colebarach/crt_xy_monitor/hardware/crt/crt.kicad_pcb

## KiCad design sch/Z80proto1(suspend)/Z80proto1_IOboard.kicad_sch

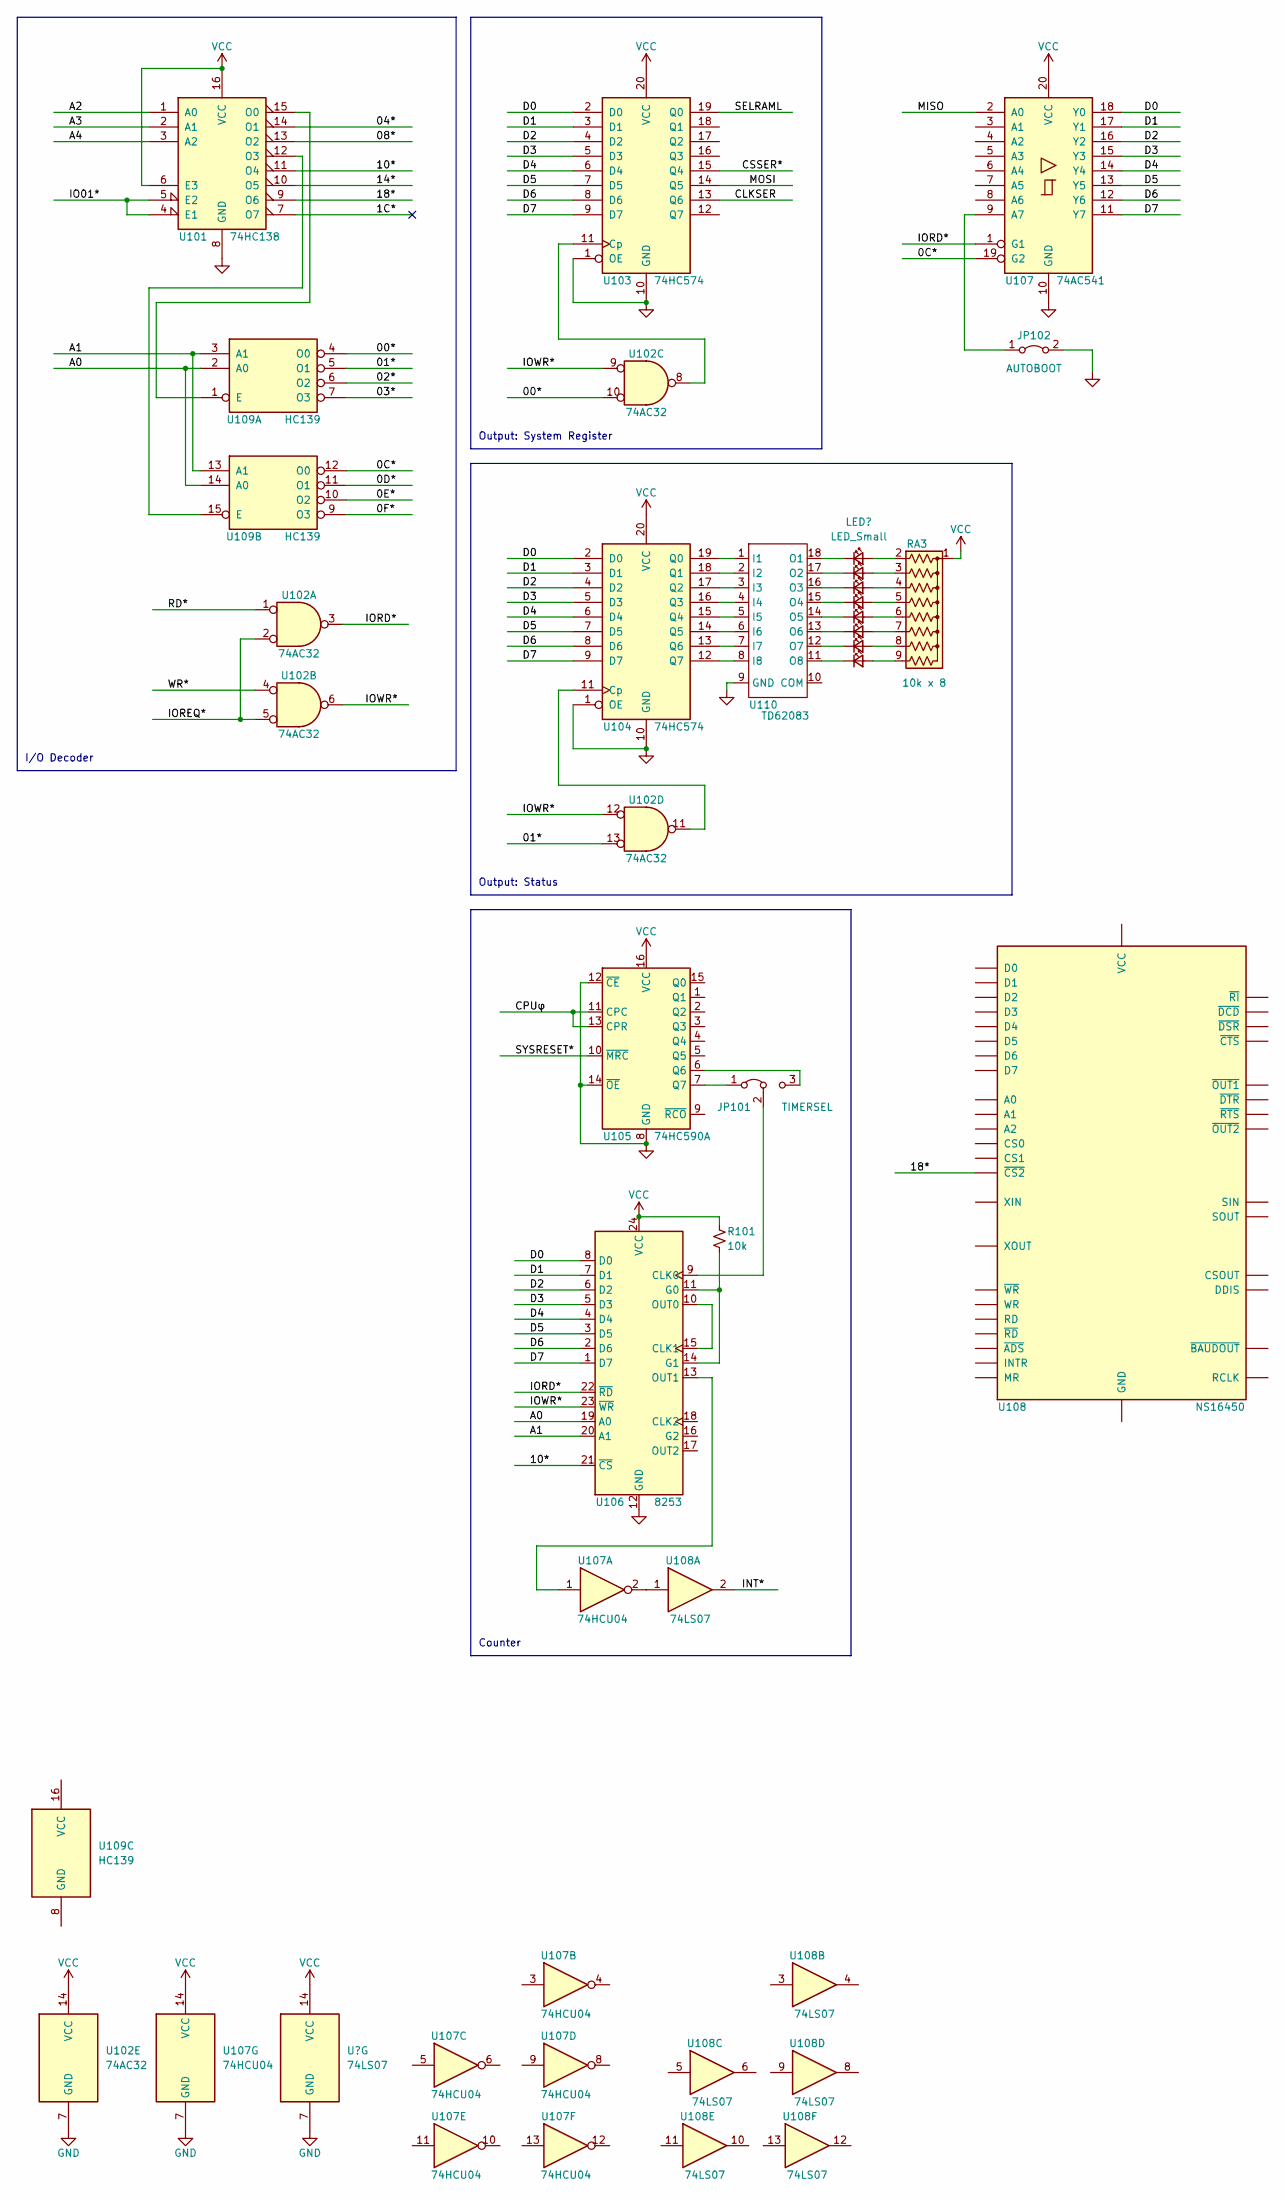
[picture p9: schematic Z80proto1_IOboard.kicad_sch]

Parts:
JP101: TIMERSEL
JP102: AUTOBOOT
R101: 10k
RA3: 10k x 8; R_Array_SIP9
U101: 74HC138
U102: 74AC32
U103, U104: 74HC574
U105: 74HC590A
U106: 8253; DIP-24_W15.24mm
U107: 74AC541
U108: 74LS07
U109: HC139
U110: TD62083

Connections:
00*: U102.10, U109.4 (O0)
0C*: U107.19 (G2), U109.12 (O0)
0D*: U109.11 (O1)
0E*: U109.10 (O2)
0F*: U109.9 (O3)
01*: U102.13, U109.5 (O1)
1C*: U101.7 (O7)
02*: U109.6 (O2)
03*: U109.7 (O3)
04*: U101.14 (O1)
08*: U101.13 (O2)
10*: U101.11 (O4), U106.21 (~CS)
14*: U101.10 (O5)
18*: U101.9 (O6), U108.14 (VCC)
A0: U106.19 (A0), U109.2 (A0), U109.14 (A0)
A1: U106.20 (A1), U109.3 (A1), U109.13 (A1)
A2: U101.1 (A0)
A3: U101.2 (A1)
A4: U101.3 (A2)
CLKSER: U103.13 (Q6)
CPUφ: U105.11 (CPC), U105.13 (CPR)
CSSER*: U103.15 (Q4)
D0: U103.2 (D0), U104.2 (D0), U106.8 (D0), U107.18 (Y0)
D1: U103.3 (D1), U104.3 (D1), U106.7 (D1), U107.17 (Y1)
D2: U103.4 (D2), U104.4 (D2), U106.6 (D2), U107.16 (Y2)
D3: U103.5 (D3), U104.5 (D3), U106.5 (D3), U107.15 (Y3)
D4: U103.6 (D4), U104.6 (D4), U106.4 (D4), U107.14 (VCC)
D5: U103.7 (D5), U104.7 (D5), U106.3 (D5), U107.13
D6: U103.8 (D6), U104.8 (D6), U106.2 (D6), U107.12
D7: U103.9 (D7), U104.9 (D7), U106.1 (D7), U107.11
INT*: U108.2
IO01*: U101.4 (E1), U101.5 (E2)
IORD*: U102.3, U106.22 (~RD), U107.1
IOREQ*: U102.2, U102.5
IOWR*: U102.6, U102.9, U102.12, U106.23 (~WR)
MISO: U107.2
MOSI: U103.14 (Q5)
unnamed: JP101.1 (A), U105.7 (Q7)
unnamed: JP101.2 (C), U106.9 (CLK0)
unnamed: JP101.3 (B), U105.6 (Q6)
unnamed: JP102.1 (A), U107.9
unnamed: R101.1, U106.24 (VCC)
unnamed: R101.2, U106.11 (G0), U106.14 (G1)
unnamed: U101.12 (O3), U109.15 (E)
unnamed: U101.15 (O0), U109.1 (E)
unnamed: U101.6 (E3), U101.16 (VCC)
unnamed: U102.8, U103.11 (Cp)
unnamed: U102.11, U104.11 (Cp)
unnamed: U103.1 (OE), U103.10 (GND)
unnamed: U104.1 (OE), U104.10 (GND)
unnamed: U104.12 (Q7), U110.8 (I8)
unnamed: U104.13 (Q6), U110.7 (I7)
unnamed: U104.14 (Q5), U110.6 (I6)
unnamed: U104.15 (Q4), U110.5 (I5)
unnamed: U104.16 (Q3), U110.4 (I4)
unnamed: U104.17 (Q2), U110.3 (I3)
unnamed: U104.18 (Q1), U110.2 (I2)
unnamed: U104.19 (Q0), U110.1 (I1)
unnamed: U105.8 (GND), U105.12 (~CE), U105.14 (~OE)
unnamed: U106.10 (OUT0), U106.15 (CLK1)
unnamed: U106.13 (OUT1), U107.1
unnamed: U107.2, U108.1
RD*: U102.1
SELRAML: U103.19 (Q0)
SYSRESET*: U105.10 (~MRC)
WR*: U102.4

Notes on the sheet:
Output: Status
I/O Decoder
Output: System Register
Counter
