colebarach/crt_xy_monitor/hardware/crt/crt.kicad_pcb

## KiCad design sch/Z80proto2/FDC_DMA.kicad_sch

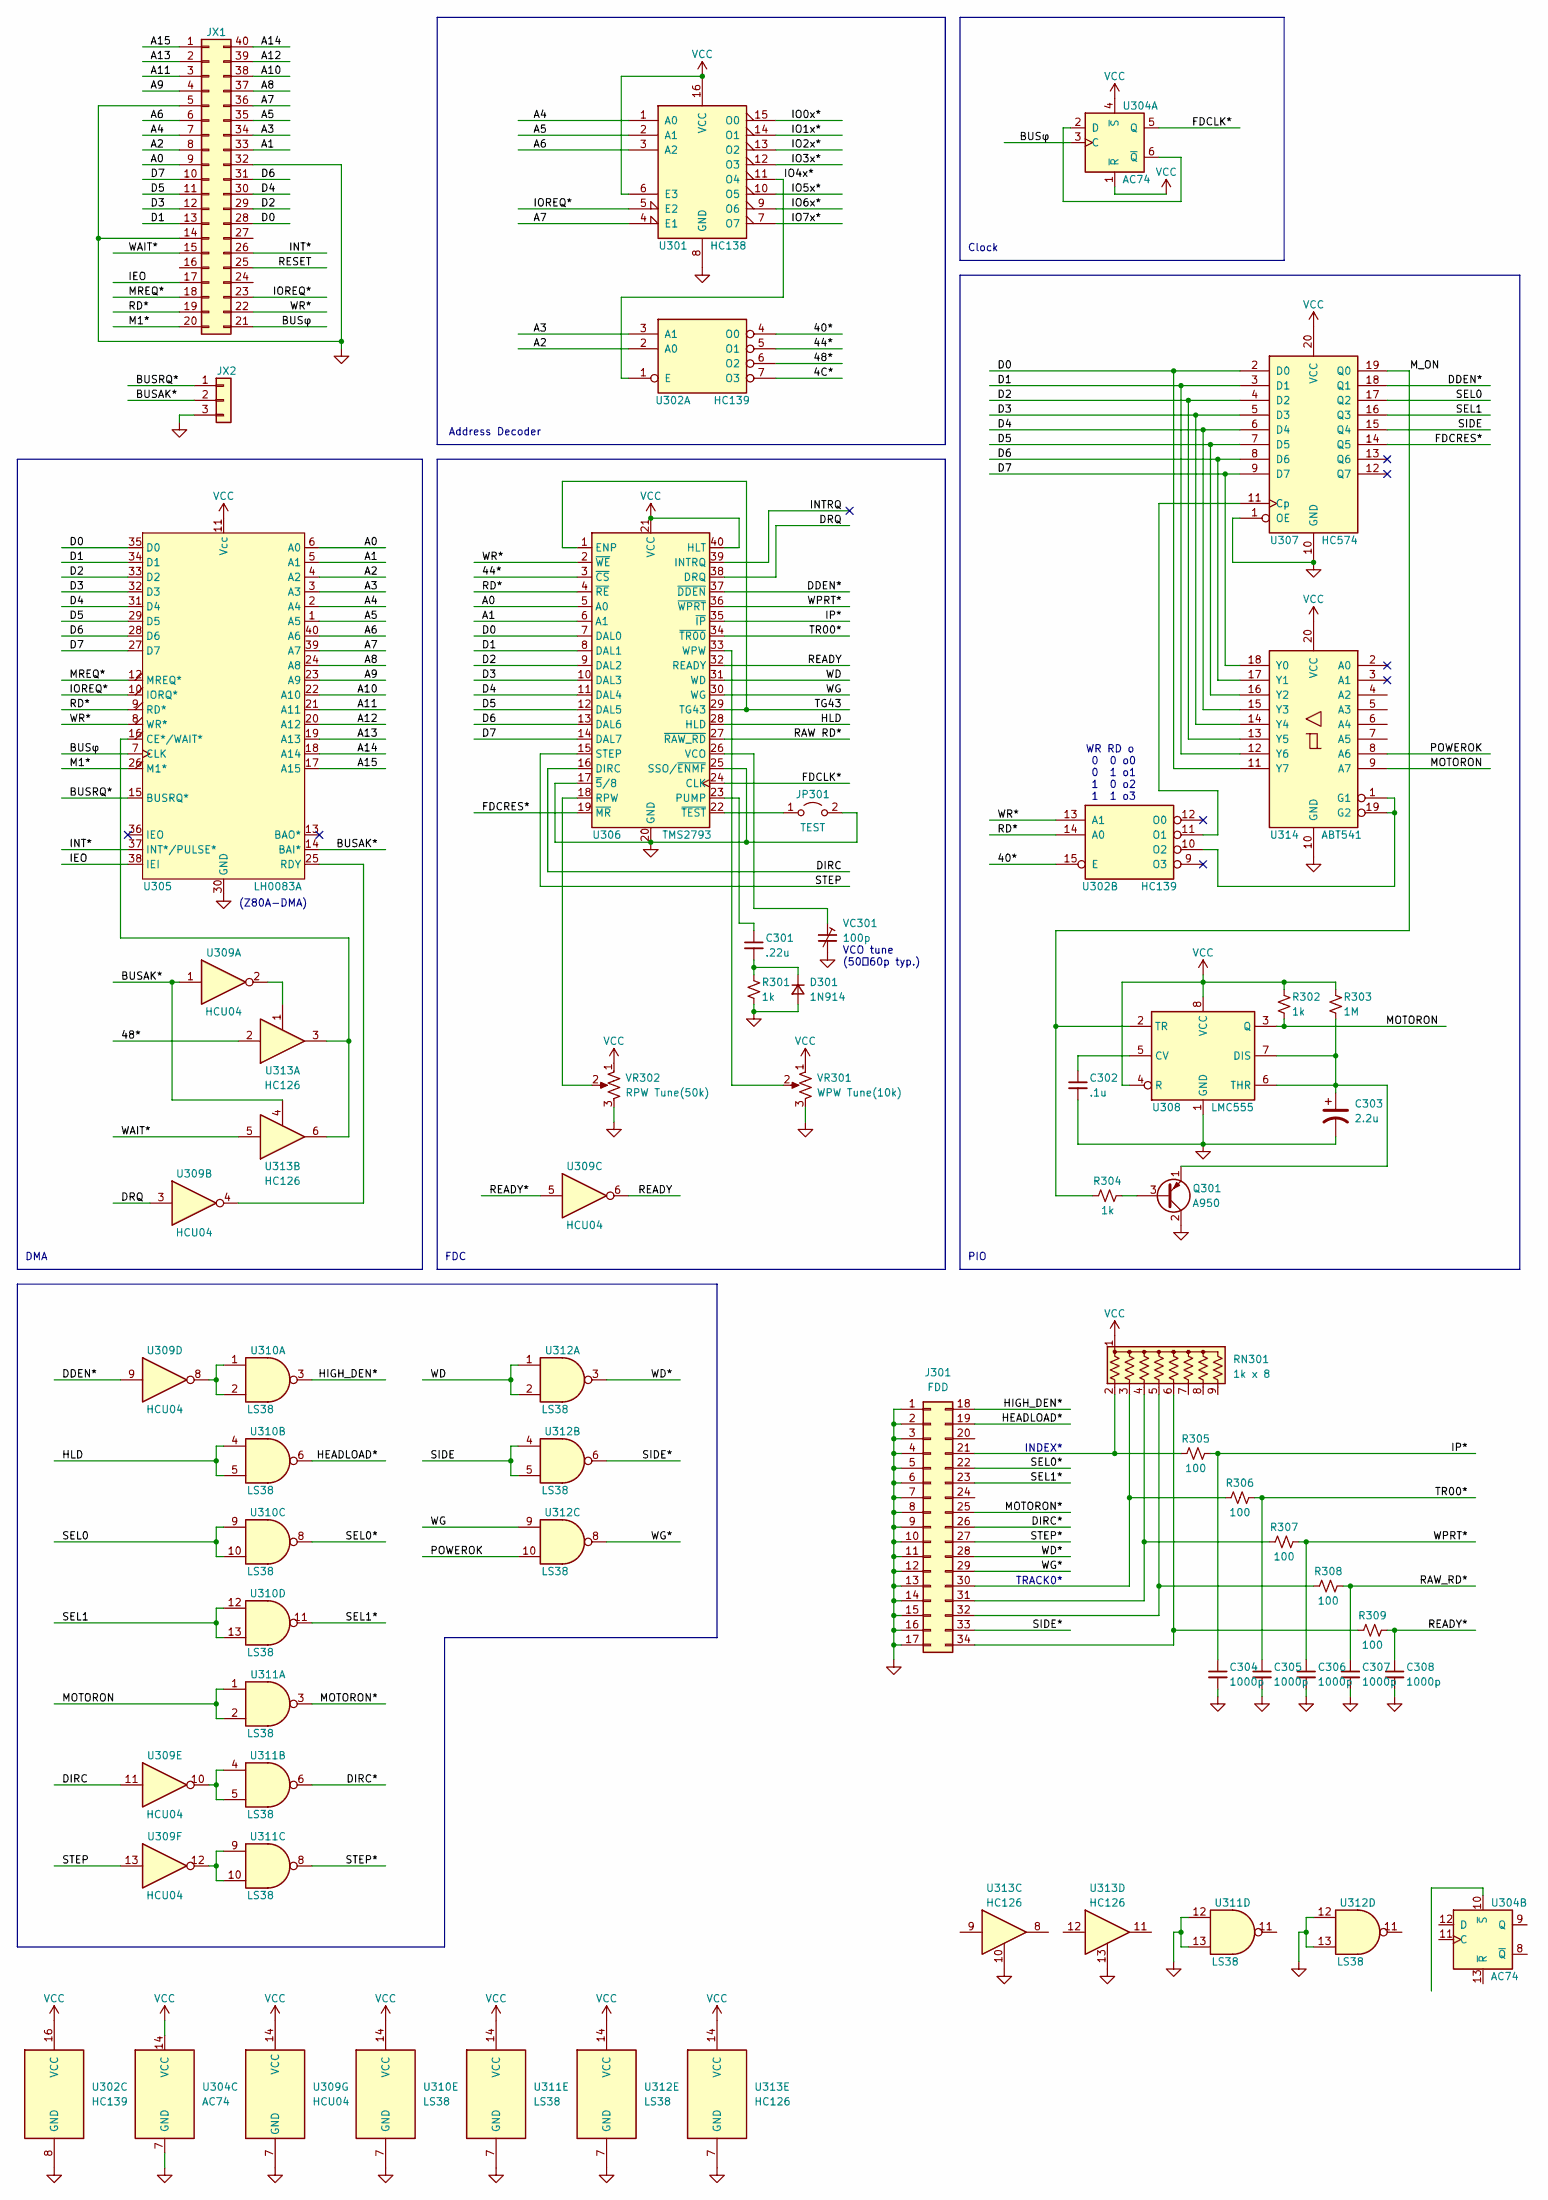
[picture p11: schematic FDC_DMA.kicad_sch]

Parts:
C301: .22u
C302: .1u
C303: 2.2u
C304, C305, C306, C307, C308: 1000p
D301: 1N914
J301: FDD
JP301: TEST
JX1: Conn_02x20_Counter_Clockwise
JX2: Conn_01x03
Q301: A950
R301, R302, R304: 1k
R303: 1M
R305, R306, R307, R308, R309: 100
RN301: 1k x 8; R_Array_SIP9
U301: HC138
U302: HC139
U304: AC74
U305: LH0083A
U306: TMS2793
U307: HC574
U308: LMC555; DIP-8_W7.62mm
U309: HCU04
U310, U311, U312: LS38
U313: HC126
U314: ABT541
VC301: 100p
VR301: WPW Tune(10k)
VR302: RPW Tune(50k)

Connections:
4C*: U302.7 (O3)
40*: U302.4 (O0), U302.15 (E)
44*: U302.5 (O1), U306.3 (~CS)
48*: U302.6 (O2), U313.2
A0: JX1.9, U305.6 (A0), U306.5 (A0)
A1: JX1.33, U305.5 (A1), U306.6 (A1)
A2: JX1.8, U302.2 (A0), U305.4 (A2)
A3: JX1.34, U302.3 (A1), U305.3 (A3)
A4: JX1.7, U301.1 (A0), U305.2 (A4)
A5: JX1.35, U301.2 (A1), U305.1 (A5)
A6: JX1.6, U301.3 (A2), U305.40 (A6)
A7: JX1.36, U301.4 (E1), U305.39 (A7)
A8: JX1.37, U305.24 (A8)
A9: JX1.4, U305.23 (A9)
A10: JX1.38, U305.22 (A10)
A11: JX1.3, U305.21 (A11)
A12: JX1.39, U305.20 (A12)
A13: JX1.2, U305.19 (A13)
A14: JX1.40, U305.18 (A14)
A15: JX1.1, U305.17 (A15)
BUSAK*: JX2.2, U305.14 (BAI*), U309.1, U313.4
BUSRQ*: JX2.1, U305.15 (BUSRQ*)
BUSφ: JX1.21, U304.3 (C), U305.7 (CLK)
D0: JX1.28, U305.35 (D0), U306.7 (DAL0), U307.2 (D0), U314.11 (Y7)
D1: JX1.13, U305.34 (D1), U306.8 (DAL1), U307.3 (D1), U314.12 (Y6)
D2: JX1.29, U305.33 (D2), U306.9 (DAL2), U307.4 (D2), U314.13 (Y5)
D3: JX1.12, U305.32 (D3), U306.10 (DAL3), U307.5 (D3), U314.14 (Y4)
D4: JX1.30, U305.31 (D4), U306.11 (DAL4), U307.6 (D4), U314.15 (Y3)
D5: JX1.11, U305.29 (D5), U306.12 (DAL5), U307.7 (D5), U314.16 (Y2)
D6: JX1.31, U305.28 (D6), U306.13 (DAL6), U307.8 (D6), U314.17 (Y1)
D7: JX1.10, U305.27 (D7), U306.14 (DAL7), U307.9 (D7), U314.18 (Y0)
DDEN*: U306.37 (~DDEN), U307.18 (Q1), U309.9
DIRC: U306.16 (DIRC), U309.11
DIRC*: J301.26, U311.6
DRQ: U306.38 (DRQ), U309.3
FDCLK*: U304.5 (Q), U306.24 (CLK)
FDCRES*: U306.19 (~MR), U307.14 (Q5)
HEADLOAD*: J301.19, U310.6
HIGH_DEN*: J301.18, U310.3
HLD: U306.28 (HLD), U310.4, U310.5
IEO: JX1.17, U305.38 (IEI)
INT*: JX1.26, U305.37 (INT*/PULSE*)
INTRQ: U306.39 (INTRQ)
IO0x*: U301.15 (O0)
IO1x*: U301.14 (O1)
IO2x*: U301.13 (O2)
IO3x*: U301.12 (O3)
IO4x*: U301.11 (O4), U302.1 (E)
IO5x*: U301.10 (O5)
IO6x*: U301.9 (O6)
IO7x*: U301.7 (O7)
IOREQ*: JX1.23, U301.5 (E2), U305.10 (IORQ*)
IP*: C304.1, R305.2, U306.35 (~IP)
M1*: JX1.20, U305.26 (M1*)
MOTORON: R302.2, U308.3 (Q), U311.1, U311.2, U314.9 (A7)
MOTORON*: J301.25, U311.3
MREQ*: JX1.18, U305.12 (MREQ*)
M_ON: R304.1, U307.19 (Q0), U308.2 (TR)
unnamed: C301.1, U306.23 (PUMP)
unnamed: C301.2, D301.1 (K), R301.1
unnamed: C302.1, U308.5 (CV)
unnamed: C302.2, C303.2, U308.1 (GND)
unnamed: C303.1, Q301.1 (E), R303.2, U308.6 (THR), U308.7 (DIS)
unnamed: D301.2 (A), R301.2
unnamed: J301.1, J301.2, J301.3, J301.4, J301.5, J301.6, J301.7, J301.8, J301.9, J301.10, J301.11, J301.12, J301.13, J301.14, J301.15, J301.16, J301.17
unnamed: J301.21, R305.1, RN301.2 (R1)
unnamed: J301.30, R306.1, RN301.3 (R2)
unnamed: J301.31, R307.1, RN301.4 (R3)
unnamed: J301.32, R308.1, RN301.5 (R4)
unnamed: J301.34, R309.1, RN301.6 (R5)
unnamed: JP301.1 (A), U306.22 (~TEST)
unnamed: JP301.2 (B), U306.17 (~5/8), U306.20 (GND), U306.25 (SSO/~ENMF)
unnamed: JX1.5, JX1.14, JX1.32
unnamed: Q301.3 (B), R304.2
unnamed: R302.1, R303.1, U308.4 (R), U308.8 (VCC)
unnamed: U301.6 (E3), U301.16 (VCC)
unnamed: U302.10 (O2), U314.1 (G1), U314.19 (G2)
unnamed: U302.11 (O1), U307.11 (Cp)
unnamed: U304.2 (D), U304.6 (~Q)
unnamed: U305.16 (CE*/WAIT*), U313.3, U313.6
unnamed: U305.25 (RDY), U309.4
unnamed: U306.18 (RPW), VR302.2
unnamed: U306.21 (VCC), U306.40 (HLT)
unnamed: U306.26 (VCO), VC301.1
unnamed: U306.33 (WPW), VR301.2
unnamed: U307.1 (OE), U307.10 (GND)
unnamed: U309.2, U313.1
unnamed: U309.8, U310.1, U310.2
unnamed: U309.10, U311.4, U311.5
unnamed: U309.12, U311.9, U311.10
unnamed: U311.12, U311.13
unnamed: U312.12, U312.13
POWEROK: U312.10, U314.8 (A6)
RAW RD*: U306.27 (~RAW_RD)
RAW_RD*: C307.1, R308.2
RD*: JX1.19, U302.14 (A0), U305.9 (RD*), U306.4 (~RE)
READY: U306.32 (READY), U309.6
READY*: C308.1, R309.2, U309.5
RESET: JX1.25
SEL0: U307.17 (Q2), U310.9, U310.10
SEL0*: J301.22, U310.8
SEL1: U307.16 (Q3), U310.12, U310.13
SEL1*: J301.23, U310.11
SIDE: U307.15 (Q4), U312.4, U312.5
SIDE*: J301.33, U312.6
STEP: U306.15 (STEP), U309.13
STEP*: J301.27, U311.8
TG43: U306.1 (ENP), U306.29 (TG43)
TR00*: C305.1, R306.2, U306.34 (~TR00)
WAIT*: JX1.15, U313.5
WD: U306.31 (WD), U312.1, U312.2
WD*: J301.28, U312.3
WG: U306.30 (WG), U312.9
WG*: J301.29, U312.8
WPRT*: C306.1, R307.2, U306.36 (~WPRT)
WR*: JX1.22, U302.13 (A1), U305.8 (WR*), U306.2 (~WE)

Notes on the sheet:
Address Decoder
(Z80A-DMA)
FDC
Clock
PIO
DMA
WR RD o 0 0 o0 0 1 o1 1 0 o2 1 1 o3
TRACK0*
INDEX*
VCO tune (50～60p typ.)
