colebarach/crt_xy_monitor/hardware/crt/crt.kicad_pcb

## KiCad design sch/Z80proto2/SPIROM_wLevelConvert.kicad_sch

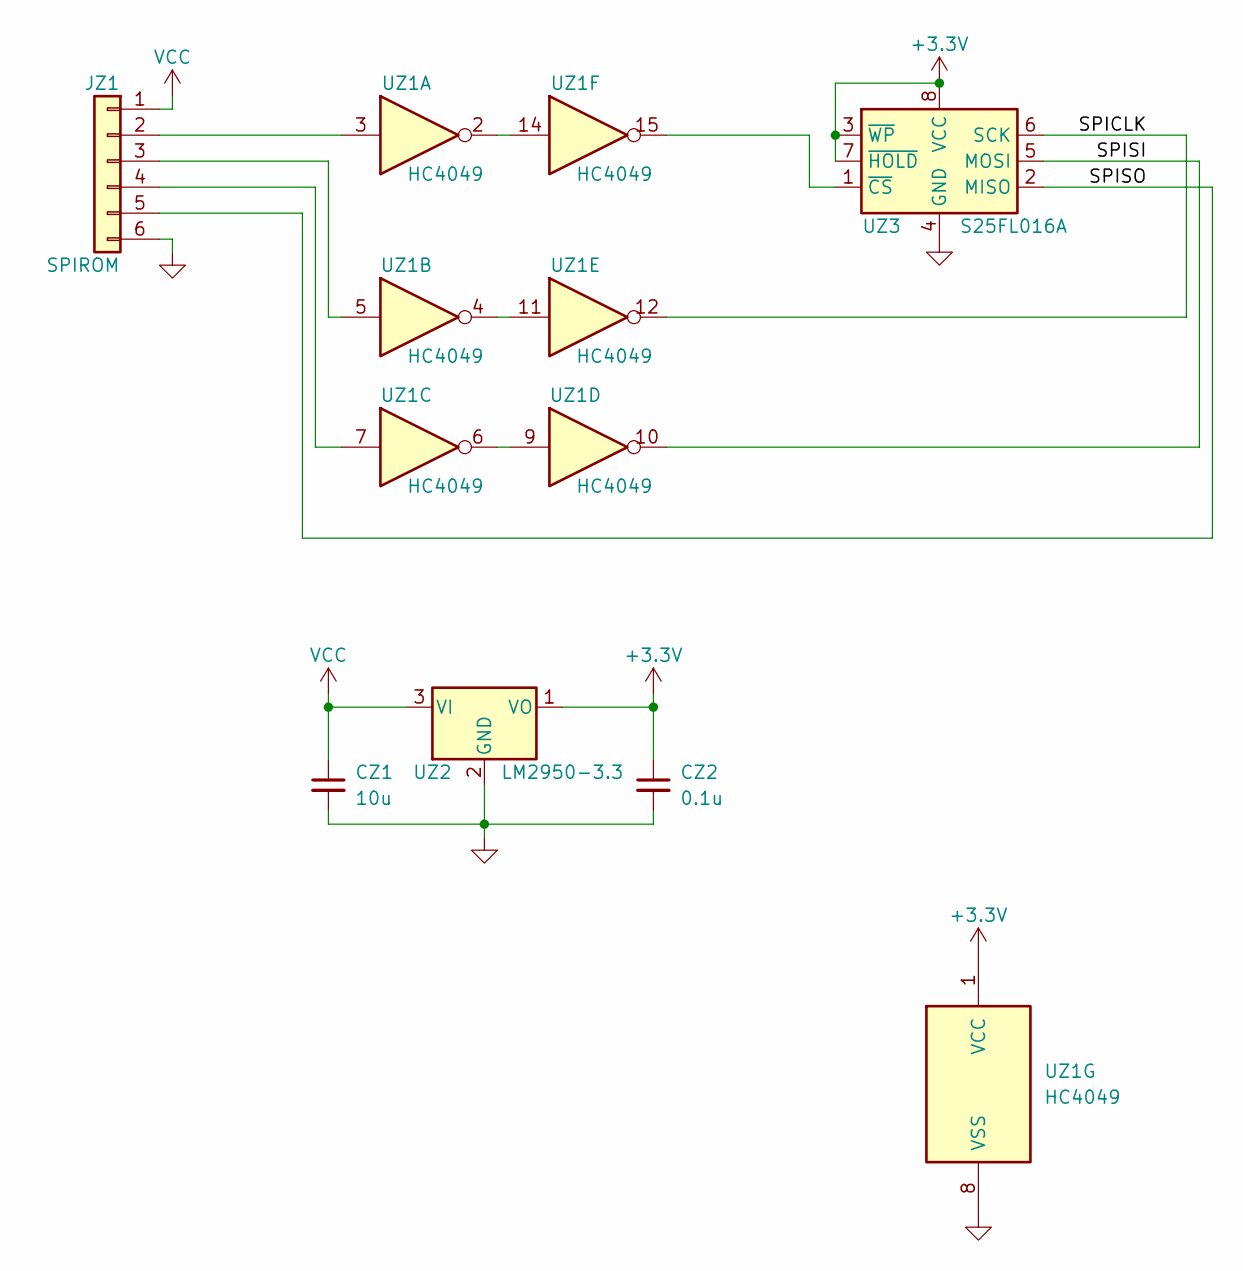
[picture p14: schematic SPIROM_wLevelConvert.kicad_sch]

Parts:
CZ1: 10u
CZ2: 0.1u
JZ1: SPIROM
UZ1: HC4049
UZ2: LM2950-3.3; TO-92_Inline
UZ3: S25FL016A

Connections:
unnamed: CZ1.1, UZ2.3 (VI)
unnamed: CZ1.2, CZ2.2, UZ2.2 (GND)
unnamed: CZ2.1, UZ2.1 (VO)
unnamed: JZ1.2, UZ1.3
unnamed: JZ1.3, UZ1.5
unnamed: JZ1.4, UZ1.7
unnamed: UZ1.6, UZ1.9
unnamed: UZ1.4, UZ1.11
unnamed: UZ1.2, UZ1.14
unnamed: UZ1.15, UZ3.1 (~CS)
unnamed: UZ3.3 (~WP), UZ3.7 (~HOLD), UZ3.8 (VCC)
SPICLK: UZ1.12, UZ3.6 (SCK)
SPISI: UZ1.10, UZ3.5 (MOSI)
SPISO: JZ1.5, UZ3.2 (MISO)
