colebarach/crt_xy_monitor/hardware/crt/crt.kicad_pcb

## KiCad design sch/Z80proto-SAKI80/Z80proto-SAKI80_IOblock.kicad_sch

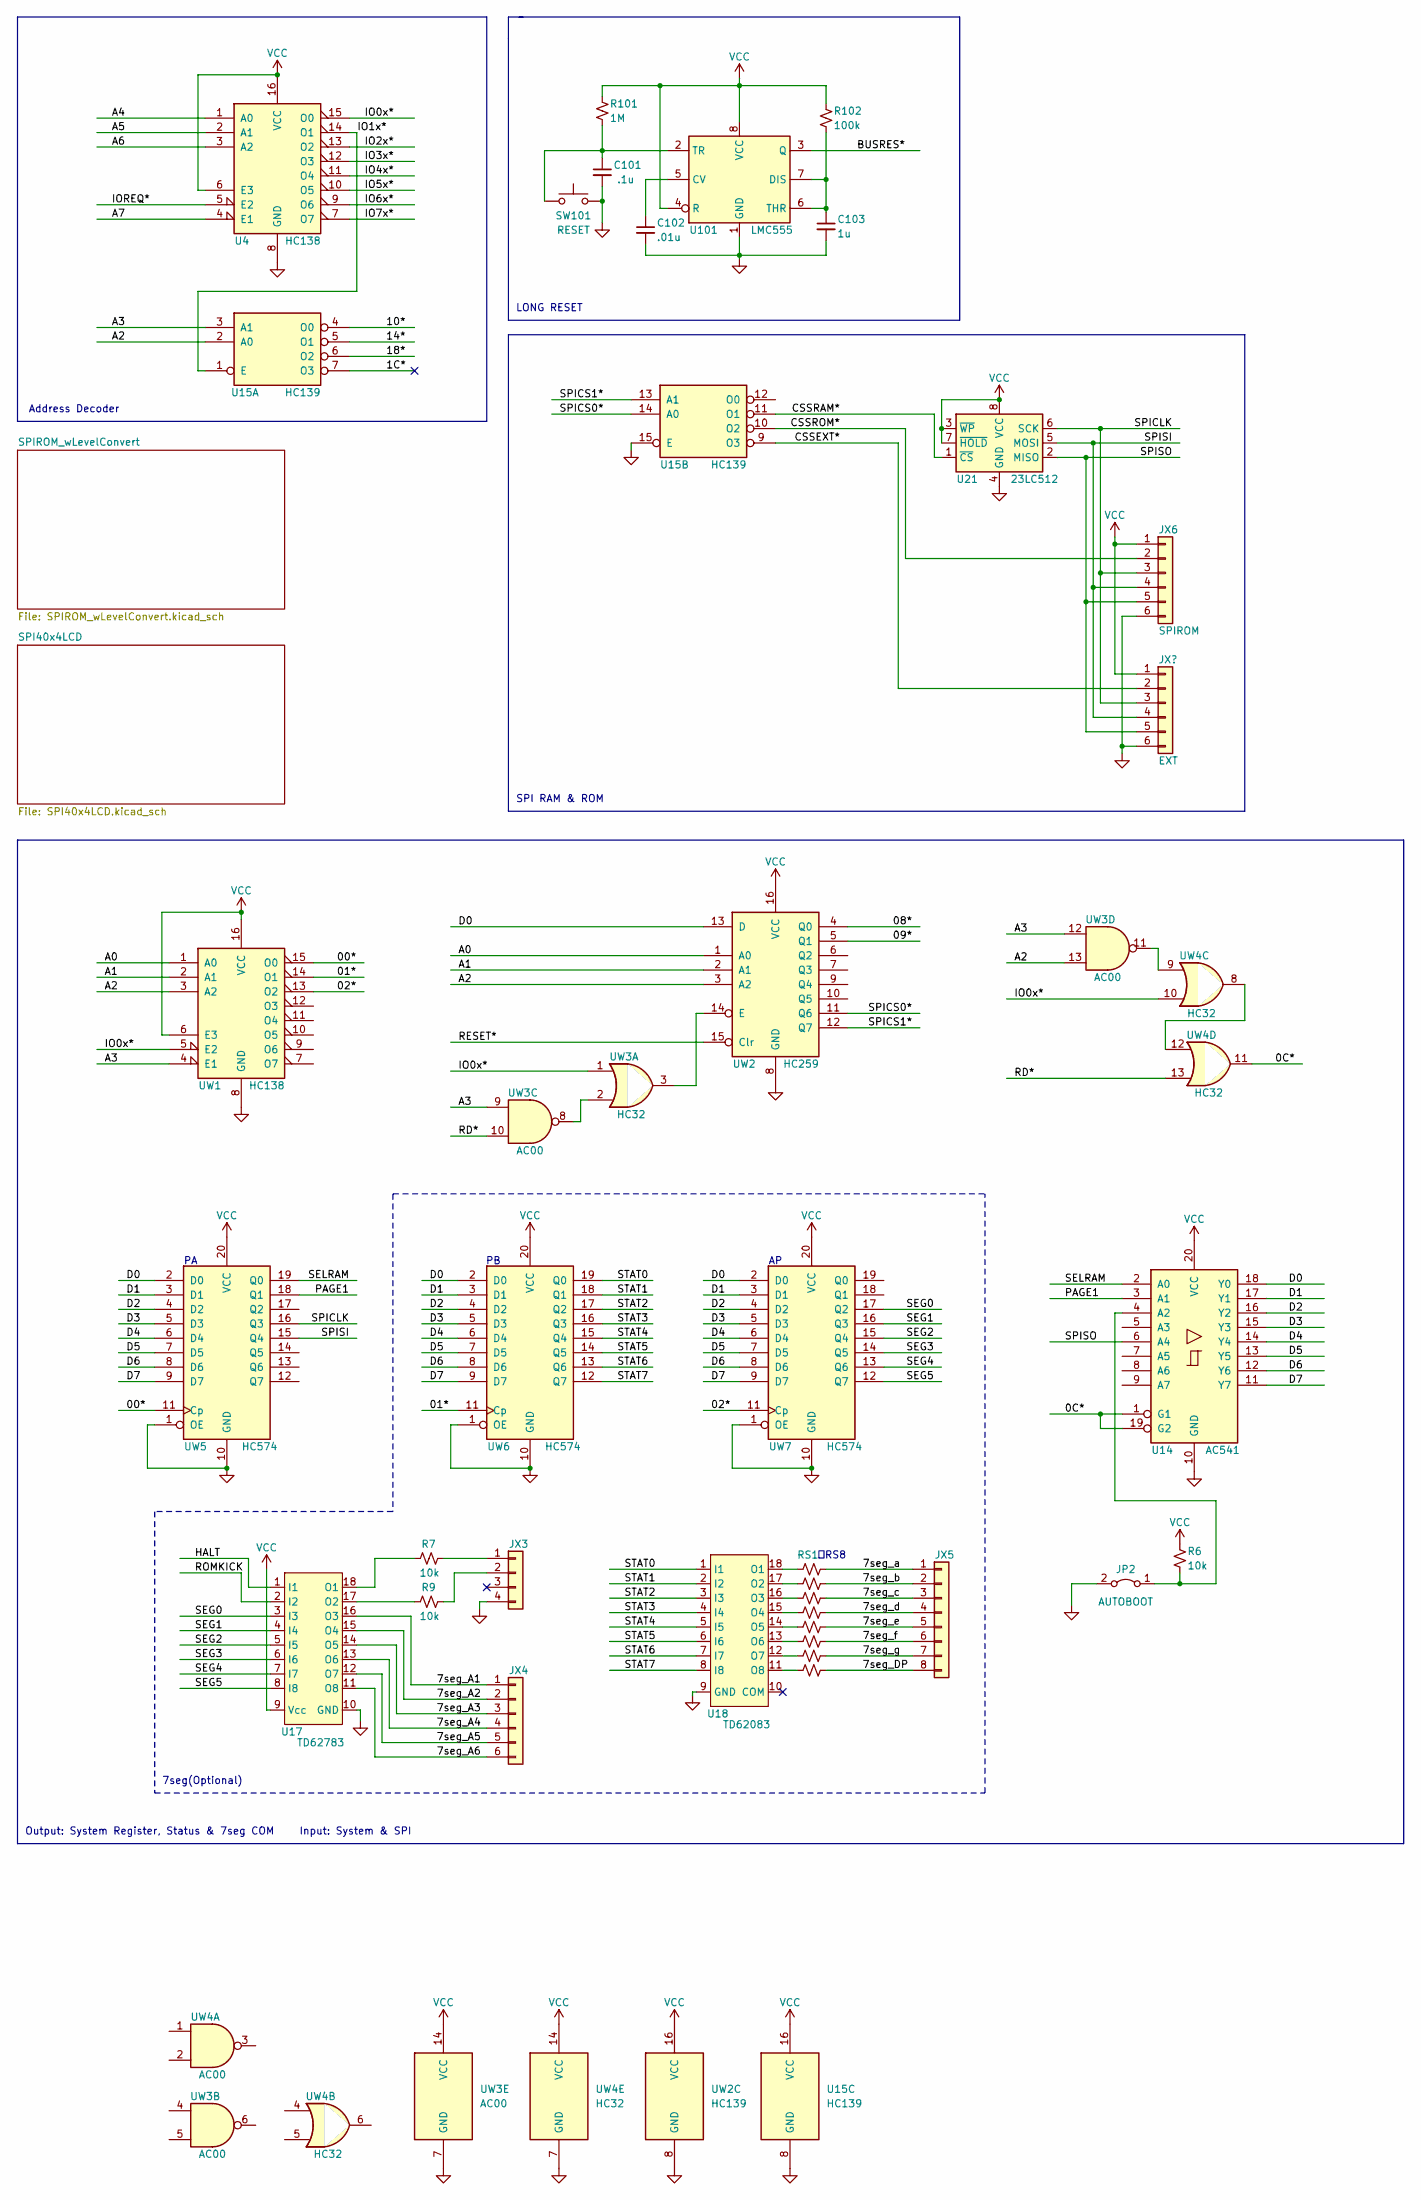
[picture p20: schematic Z80proto-SAKI80_IOblock.kicad_sch]

Parts:
C101: .1u
C102: .01u
C103: 1u
JP2: AUTOBOOT
JX3: Conn_01x04
JX4: Conn_01x06
JX5: Conn_01x08
JX6: SPIROM
R6, R7, R9: 10k
R101: 1M
R102: 100k
RS1, RS2, RS3, RS4, RS5, RS6, RS7, RS8: 1k
SW101: RESET
U4: HC138
U14: AC541
U15: HC139
U17: TD62783
U18: TD62083
U21: 23LC512
U101: LMC555; DIP-8_W7.62mm
UW1: HC138
UW2: HC139
UW3: AC00
UW4: HC32
UW5, UW6, UW7: HC574

Connections:
00*: UW1.15 (O0), UW5.11 (Cp)
0C*: U14.1 (G1), U14.19 (G2), UW4.11
01*: UW1.14 (O1), UW6.11 (Cp)
1C*: U15.7 (O3)
02*: UW1.13 (O2), UW7.11 (Cp)
7seg_A1: JX4.1, U17.16 (O3)
7seg_A2: JX4.2, U17.15 (O4)
7seg_A3: JX4.3, U17.14 (O5)
7seg_A4: JX4.4, U17.13 (O6)
7seg_A5: JX4.5, U17.12 (O7)
7seg_A6: JX4.6, U17.11 (O8)
7seg_DP: JX5.8, RS8.2
7seg_a: JX5.1, RS1.2
7seg_b: JX5.2, RS2.2
7seg_c: JX5.3, RS3.2
7seg_d: JX5.4, RS4.2
7seg_e: JX5.5, RS5.2
7seg_f: JX5.6, RS6.2
7seg_g: JX5.7, RS7.2
08*: UW2.4 (Q0)
09*: UW2.5 (Q1)
10*: U15.4 (O0)
14*: U15.5 (O1)
18*: U15.6 (O2)
A0: UW1.1 (A0), UW2.1 (A0)
A1: UW1.2 (A1), UW2.2 (A1)
A2: U15.2 (A0), UW1.3 (A2), UW2.3 (A2), UW3.13
A3: U15.3 (A1), UW1.4 (E1), UW3.9, UW3.12
A4: U4.1 (A0)
A5: U4.2 (A1)
A6: U4.3 (A2)
A7: U4.4 (E1)
BUSRES*: U101.3 (Q)
CSSEXT*: U15.9 (O3)
CSSRAM*: U15.11 (O1), U21.1 (~CS)
CSSROM*: JX6.2, U15.10 (O2)
D0: U14.18 (Y0), UW2.13 (D), UW5.2 (D0), UW6.2 (D0), UW7.2 (D0)
D1: U14.17 (Y1), UW5.3 (D1), UW6.3 (D1), UW7.3 (D1)
D2: U14.16 (Y2), UW5.4 (D2), UW6.4 (D2), UW7.4 (D2)
D3: U14.15 (Y3), UW5.5 (D3), UW6.5 (D3), UW7.5 (D3)
D4: U14.14 (Y4), UW5.6 (D4), UW6.6 (D4), UW7.6 (D4)
D5: U14.13 (Y5), UW5.7 (D5), UW6.7 (D5), UW7.7 (D5)
D6: U14.12 (Y6), UW5.8 (D6), UW6.8 (D6), UW7.8 (D6)
D7: U14.11 (Y7), UW5.9 (D7), UW6.9 (D7), UW7.9 (D7)
HALT: U17.1 (I1)
IO0x*: U4.15 (O0), UW1.5 (E2), UW3.1, UW4.10
IO1x*: U4.14 (O1), U15.1 (E)
IO2x*: U4.13 (O2)
IO3x*: U4.12 (O3)
IO4x*: U4.11 (O4)
IO5x*: U4.10 (O5)
IO6x*: U4.9 (O6)
IO7x*: U4.7 (O7)
IOREQ*: U4.5 (E2)
unnamed: C101.1, R101.2, SW101.1, U101.2 (TR)
unnamed: C101.2, SW101.2
unnamed: C102.1, U101.5 (CV)
unnamed: C102.2, C103.2, U101.1 (GND)
unnamed: C103.1, R102.2, U101.6 (THR), U101.7 (DIS)
unnamed: JP2.1 (A), R6.2, U14.4 (A2)
unnamed: JX3.1, R7.2
unnamed: JX3.2, R9.2
unnamed: R7.1, U17.18 (O1)
unnamed: R9.1, U17.17 (O2)
unnamed: R101.1, R102.1, U101.4 (R), U101.8 (VCC)
unnamed: RS1.1, U18.18 (O1)
unnamed: RS2.1, U18.17 (O2)
unnamed: RS3.1, U18.16 (O3)
unnamed: RS4.1, U18.15 (O4)
unnamed: RS5.1, U18.14 (O5)
unnamed: RS6.1, U18.13 (O6)
unnamed: RS7.1, U18.12 (O7)
unnamed: RS8.1, U18.11 (O8)
unnamed: U4.6 (E3), U4.16 (VCC)
unnamed: U21.3 (~WP), U21.7 (~HOLD), U21.8 (VCC)
unnamed: UW1.6 (E3), UW1.16 (VCC)
unnamed: UW2.14 (E), UW3.3
unnamed: UW3.2, UW3.8
unnamed: UW3.11, UW4.9
unnamed: UW4.8, UW4.12
unnamed: UW5.1 (OE), UW5.10 (GND)
unnamed: UW6.1 (OE), UW6.10 (GND)
unnamed: UW7.1 (OE), UW7.10 (GND)
PAGE1: U14.3 (A1), UW5.18 (Q1)
RD*: UW3.10, UW4.13
RESET*: UW2.15 (Clr)
ROMKICK: U17.2 (I2)
SEG0: U17.3 (I3), UW7.17 (Q2)
SEG1: U17.4 (I4), UW7.16 (Q3)
SEG2: U17.5 (I5), UW7.15 (Q4)
SEG3: U17.6 (I6), UW7.14 (Q5)
SEG4: U17.7 (I7), UW7.13 (Q6)
SEG5: U17.8 (I8), UW7.12 (Q7)
SELRAM: U14.2 (A0), UW5.19 (Q0)
SPICLK: JX6.3, U21.6 (SCK), UW5.16 (Q3)
SPICS0*: U15.14 (A0), UW2.11 (Q6)
SPICS1*: U15.13 (A1), UW2.12 (Q7)
SPISI: JX6.4, U21.5 (MOSI), UW5.15 (Q4)
SPISO: JX6.5, U14.6 (A4), U21.2 (MISO)
STAT0: U18.1 (I1), UW6.19 (Q0)
STAT1: U18.2 (I2), UW6.18 (Q1)
STAT2: U18.3 (I3), UW6.17 (Q2)
STAT3: U18.4 (I4), UW6.16 (Q3)
STAT4: U18.5 (I5), UW6.15 (Q4)
STAT5: U18.6 (I6), UW6.14 (Q5)
STAT6: U18.7 (I7), UW6.13 (Q6)
STAT7: U18.8 (I8), UW6.12 (Q7)

Notes on the sheet:
SPI RAM & ROM
Output: System Register, Status & 7seg COM
LONG RESET
Input: System & SPI
～RS8
Address Decoder
7seg(Optional)
