colebarach/crt_xy_monitor/hardware/crt/crt.kicad_pcb

## KiCad design sch/MZ80K_framebuf/MZ80K_framebuf/MZ80K_framebuf.kicad_sch

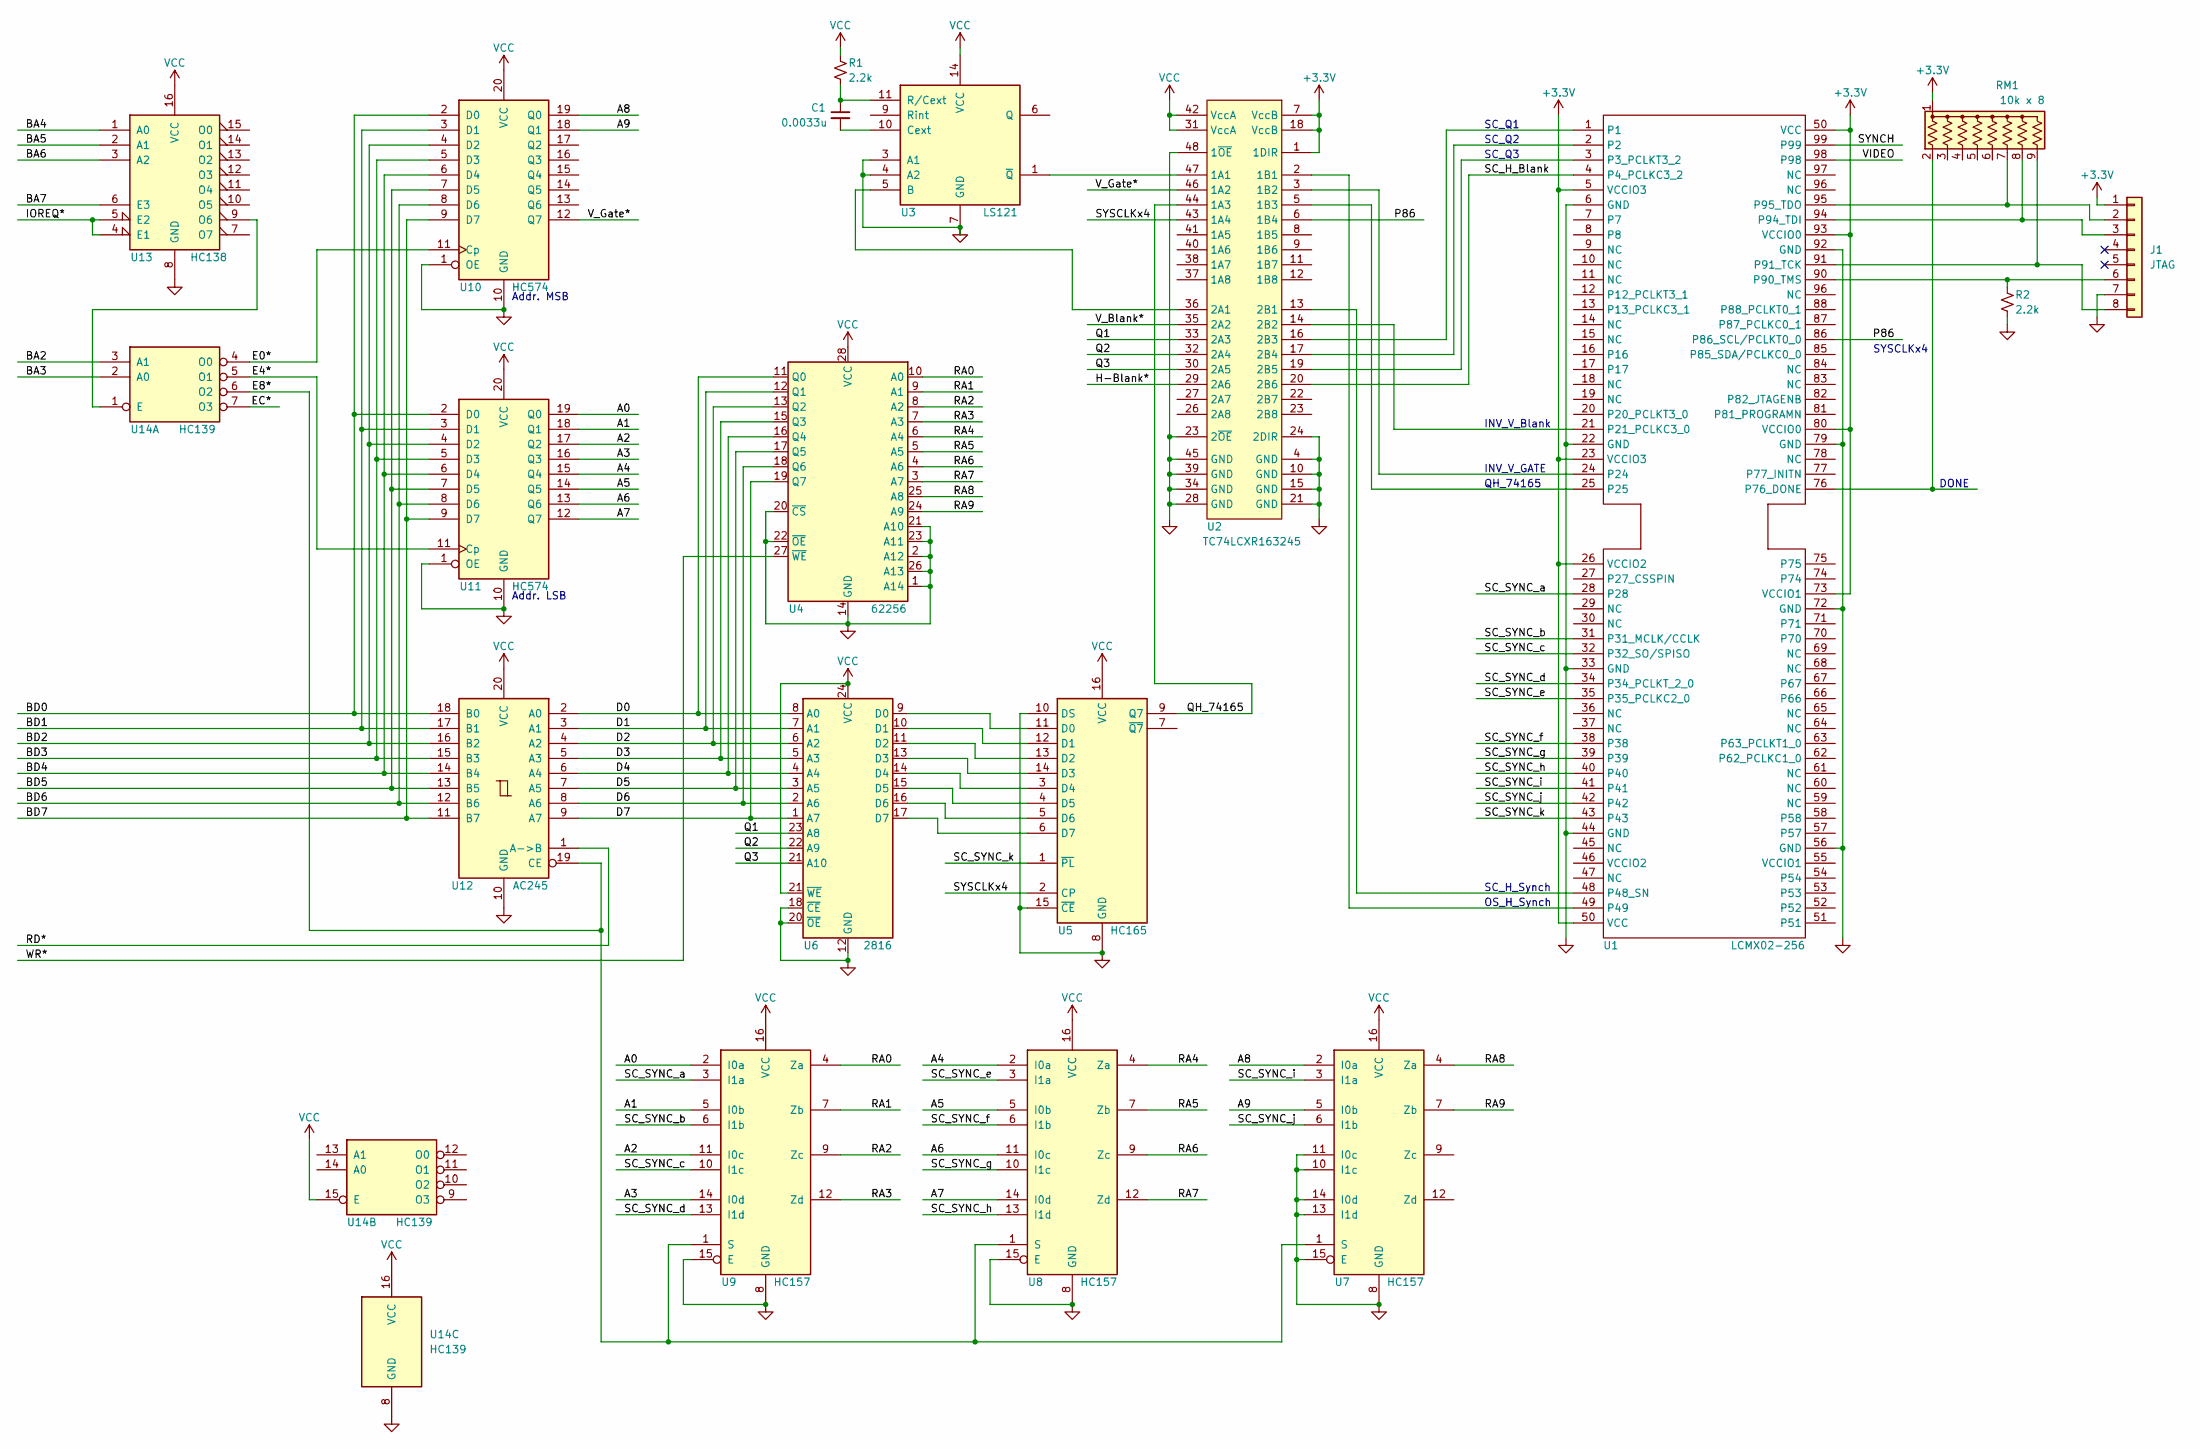
[picture p23: schematic MZ80K_framebuf.kicad_sch]

Parts:
C1: 0.0033u
J1: JTAG
R1, R2: 2.2k
RM1: 10k x 8; R_Array_SIP9
U1: LCMX02-256
U2: TC74LCXR163245
U3: LS121
U4: 62256; DIP-28_W15.24mm
U5: HC165
U6: 2816
U7, U8, U9: HC157
U10, U11: HC574
U12: AC245
U13: HC138
U14: HC139

Connections:
A0: U9.2 (I0a), U11.19 (Q0)
A1: U9.5 (I0b), U11.18 (Q1)
A2: U9.11 (I0c), U11.17 (Q2)
A3: U9.14 (I0d), U11.16 (Q3)
A4: U8.2 (I0a), U11.15 (Q4)
A5: U8.5 (I0b), U11.14 (Q5)
A6: U8.11 (I0c), U11.13 (Q6)
A7: U8.14 (I0d), U11.12 (Q7)
A8: U7.2 (I0a), U10.19 (Q0)
A9: U7.5 (I0b), U10.18 (Q1)
BA2: U14.3 (A1)
BA3: U14.2 (A0)
BA4: U13.1 (A0)
BA5: U13.2 (A1)
BA6: U13.3 (A2)
BA7: U13.6 (E3)
BD0: U10.2 (D0), U11.2 (D0), U12.18 (B0)
BD1: U10.3 (D1), U11.3 (D1), U12.17 (B1)
BD2: U10.4 (D2), U11.4 (D2), U12.16 (B2)
BD3: U10.5 (D3), U11.5 (D3), U12.15 (B3)
BD4: U10.6 (D4), U11.6 (D4), U12.14 (B4)
BD5: U10.7 (D5), U11.7 (D5), U12.13 (B5)
BD6: U10.8 (D6), U11.8 (D6), U12.12 (B6)
BD7: U10.9 (D7), U11.9 (D7), U12.11 (B7)
D0: U4.11 (Q0), U6.8 (A0), U12.2 (A0)
D1: U4.12 (Q1), U6.7 (A1), U12.3 (A1)
D2: U4.13 (Q2), U6.6 (A2), U12.4 (A2)
D3: U4.15 (Q3), U6.5 (A3), U12.5 (A3)
D4: U4.16 (Q4), U6.4 (A4), U12.6 (A4)
D5: U4.17 (Q5), U6.3 (A5), U12.7 (A5)
D6: U4.18 (Q6), U6.2 (A6), U12.8 (A6)
D7: U4.19 (Q7), U6.1 (A7), U12.9 (A7)
E0*: U10.11 (Cp), U14.4 (O0)
E4*: U11.11 (Cp), U14.5 (O1)
E8*: U7.1 (S), U8.1 (S), U9.1 (S), U12.19 (CE), U14.6 (O2)
EC*: U14.7 (O3)
H-Blank*: U2.29 (2A6)
IOREQ*: U13.4 (E1), U13.5 (E2)
unnamed: C1.1, R1.2, U3.11 (R/Cext)
unnamed: C1.2, U3.10 (Cext)
unnamed: J1.2, RM1.7 (R6), U1.95 (P95_TDO)
unnamed: J1.3, RM1.8 (R7), U1.94 (P94_TDI)
unnamed: J1.6, R2.1, U1.90 (P90_TMS)
unnamed: J1.8, RM1.9 (R8), U1.91 (P91_TCK)
unnamed: RM1.2 (R1), U1.76 (P76_DONE)
unnamed: U1.1, U2.16 (2B3)
unnamed: U1.2, U2.17 (2B4)
unnamed: U1.3 (P3_PCLKT3_2), U2.19 (2B5)
unnamed: U1.21 (P21_PCLKC3_0), U2.14 (2B2)
unnamed: U1.6 (GND), U1.22 (GND), U1.33 (GND), U1.44 (GND)
unnamed: U1.5 (VCCIO3), U1.23 (VCCIO3), U1.26 (VCCIO2), U1.50 (VCC)
unnamed: U1.24, U2.3 (1B2)
unnamed: U1.25, U2.5 (1B3)
unnamed: U1.48 (P48_SN), U2.13 (2B1)
unnamed: U1.49, U2.2 (1B1)
unnamed: U1.50 (VCC), U1.73 (VCCIO1), U1.80 (VCCIO0), U1.93 (VCCIO0)
unnamed: U1.56 (GND), U1.72 (GND), U1.79 (GND), U1.92 (GND)
unnamed: U2.1 (1DIR), U2.7 (VccB), U2.18 (VccB)
unnamed: U2.4 (GND), U2.10 (GND), U2.15 (GND), U2.21 (GND), U2.24 (2DIR)
unnamed: U2.23 (2B8), U2.28 (GND), U2.34 (GND), U2.39 (GND), U2.45 (GND), U2.48 (1~OE)
unnamed: U2.31 (VccA), U2.42 (VccA)
unnamed: U2.36 (2A1), U3.5 (B)
unnamed: U2.47 (1A1), U3.1 (~Q)
unnamed: U3.3 (A1), U3.4 (A2), U3.7 (GND)
unnamed: U4.1 (A14), U4.2 (A12), U4.14 (GND), U4.20 (~CS), U4.21 (A10), U4.22 (~OE), U4.23 (A11), U4.26 (A13)
unnamed: U5.3 (D4), U6.14 (D4)
unnamed: U5.4 (D5), U6.15 (D5)
unnamed: U5.5 (D6), U6.16 (D6)
unnamed: U5.6 (D7), U6.17 (D7)
unnamed: U5.8 (GND), U5.10 (DS), U5.15 (~CE)
unnamed: U5.11 (D0), U6.9 (D0)
unnamed: U5.12 (D1), U6.10 (D1)
unnamed: U5.13 (D2), U6.11 (D2)
unnamed: U5.14 (D3), U6.13 (D3)
unnamed: U6.12 (GND), U6.18 (~CE), U6.20 (~OE)
unnamed: U6.21 (A10), U6.24 (VCC)
unnamed: U7.8 (GND), U7.10 (I1c), U7.11 (I0c), U7.13 (I1d), U7.14 (I0d), U7.15 (E)
unnamed: U8.8 (GND), U8.15 (E)
unnamed: U9.8 (GND), U9.15 (E)
unnamed: U10.1 (OE), U10.10 (GND)
unnamed: U11.1 (OE), U11.10 (GND)
unnamed: U13.9 (O6), U14.1 (E)
P86: U1.86 (P86_SCL/PCLKT0_0), U2.6 (1B4)
Q1: U2.33 (2A3), U6.23 (A8)
Q2: U2.32 (2A4), U6.22 (A9)
Q3: U2.30 (2A5), U6.21 (A10)
QH_74165: U2.44 (1A3), U5.9 (Q7)
RA0: U4.10 (A0), U9.4 (Za)
RA1: U4.9 (A1), U9.7 (Zb)
RA2: U4.8 (A2), U9.9 (Zc)
RA3: U4.7 (A3), U9.12 (Zd)
RA4: U4.6 (A4), U8.4 (Za)
RA5: U4.5 (A5), U8.7 (Zb)
RA6: U4.4 (A6), U8.9 (Zc)
RA7: U4.3 (A7), U8.12 (Zd)
RA8: U4.25 (A8), U7.4 (Za)
RA9: U4.24 (A9), U7.7 (Zb)
RD*: U12.1 (A->B)
SC_H_Blank: U1.4 (P4_PCLKC3_2), U2.20 (2B6)
SC_SYNC_a: U1.28, U9.3 (I1a)
SC_SYNC_b: U1.31 (P31_MCLK/CCLK), U9.6 (I1b)
SC_SYNC_c: U1.32 (P32_SO/SPISO), U9.10 (I1c)
SC_SYNC_d: U1.34 (P34_PCLKT_2_0), U9.13 (I1d)
SC_SYNC_e: U1.35 (P35_PCLKC2_0), U8.3 (I1a)
SC_SYNC_f: U1.38, U8.6 (I1b)
SC_SYNC_g: U1.39, U8.10 (I1c)
SC_SYNC_h: U1.40, U8.13 (I1d)
SC_SYNC_i: U1.41, U7.3 (I1a)
SC_SYNC_j: U1.42, U7.6 (I1b)
SC_SYNC_k: U1.43, U5.1 (~PL)
SYNCH: U1.99
SYSCLKx4: U2.43 (1A4), U5.2 (CP)
VIDEO: U1.98
V_Blank*: U2.35 (2A2)
V_Gate*: U2.46 (1A2), U10.12 (Q7)
WR*: U4.27 (~WE)

Notes on the sheet:
Addr. MSB
Addr. LSB
OS_H_Synch
SYSCLKx4
SC_H_Synch
SC_Q2
DONE
INV_V_GATE
SC_Q1
INV_V_Blank
QH_74165
SC_Q3
